HTangl/HTangl-Controller/Pictures/Melee Layout.png

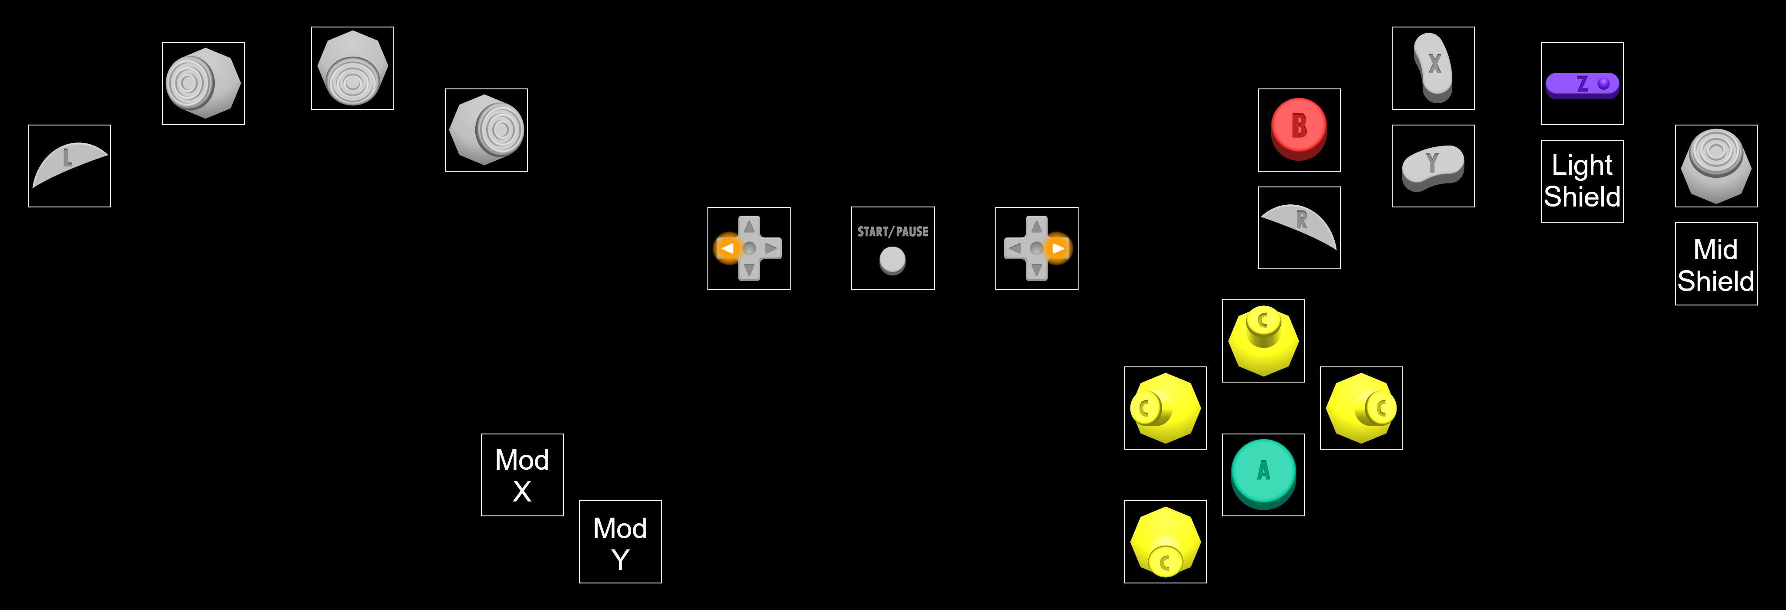
Pictures/Melee Layout.png
