HTangl/HTangl-Controller/Pictures/Version 2/Ports.jpg

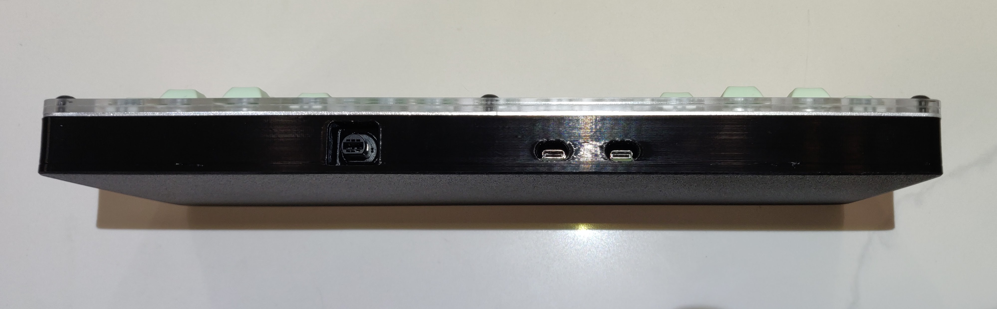
Pictures/Version 2/Ports.jpg
