HTangl/HTangl-Controller/Pictures/Version 2/Stack 3.jpg

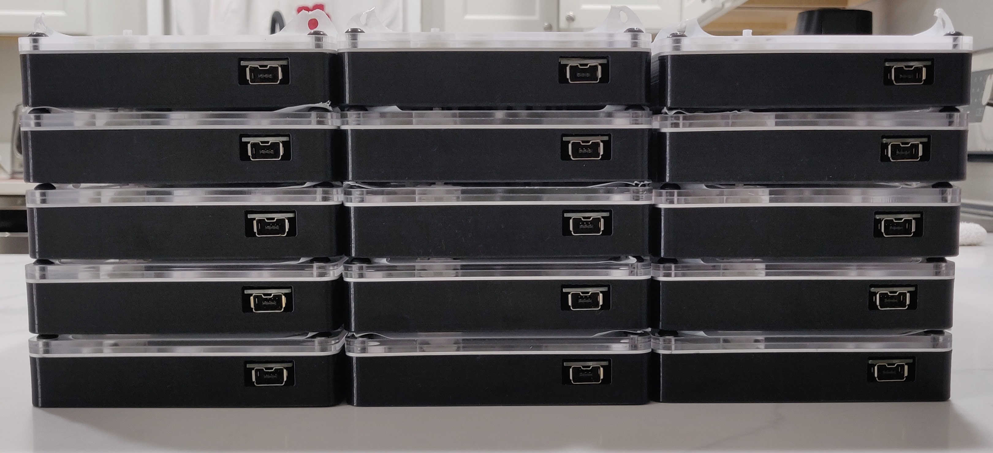
Pictures/Version 2/Stack 3.jpg
